tolbier/semaforo_ruido/PCBs/leds_PCB/leds_PCB_etch_copper_bottom.jpg

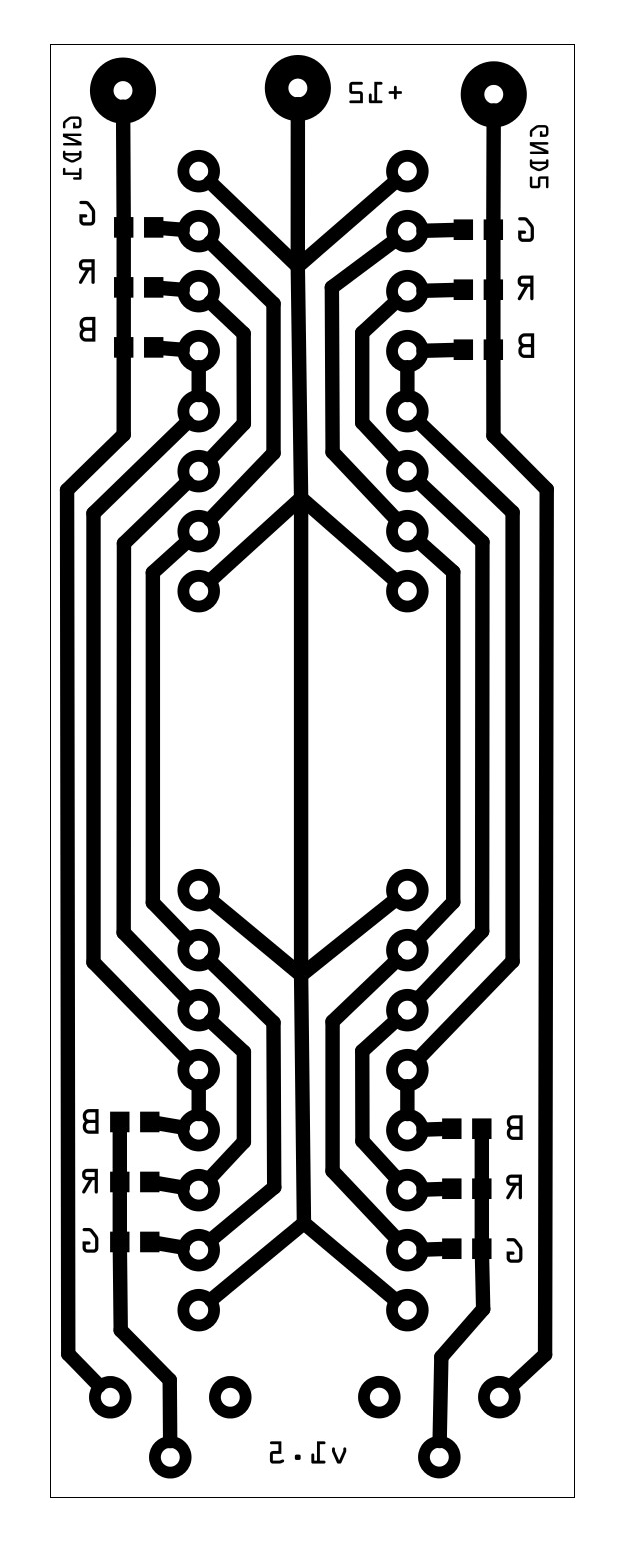
PCBs/leds_PCB/leds_PCB_etch_copper_bottom.jpg
