tolbier/semaforo_ruido/PCBs/leds_PCB/leds_PCB_pcb.jpg

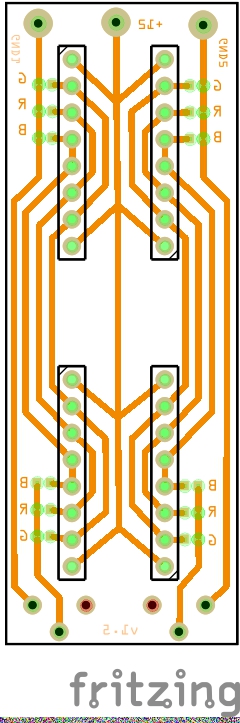
PCBs/leds_PCB/leds_PCB_pcb.jpg
