tolbier/semaforo_ruido/PCBs/semaforo_ruido_MainPCB/semaforo_ruido_MainPCB_esquema.jpg

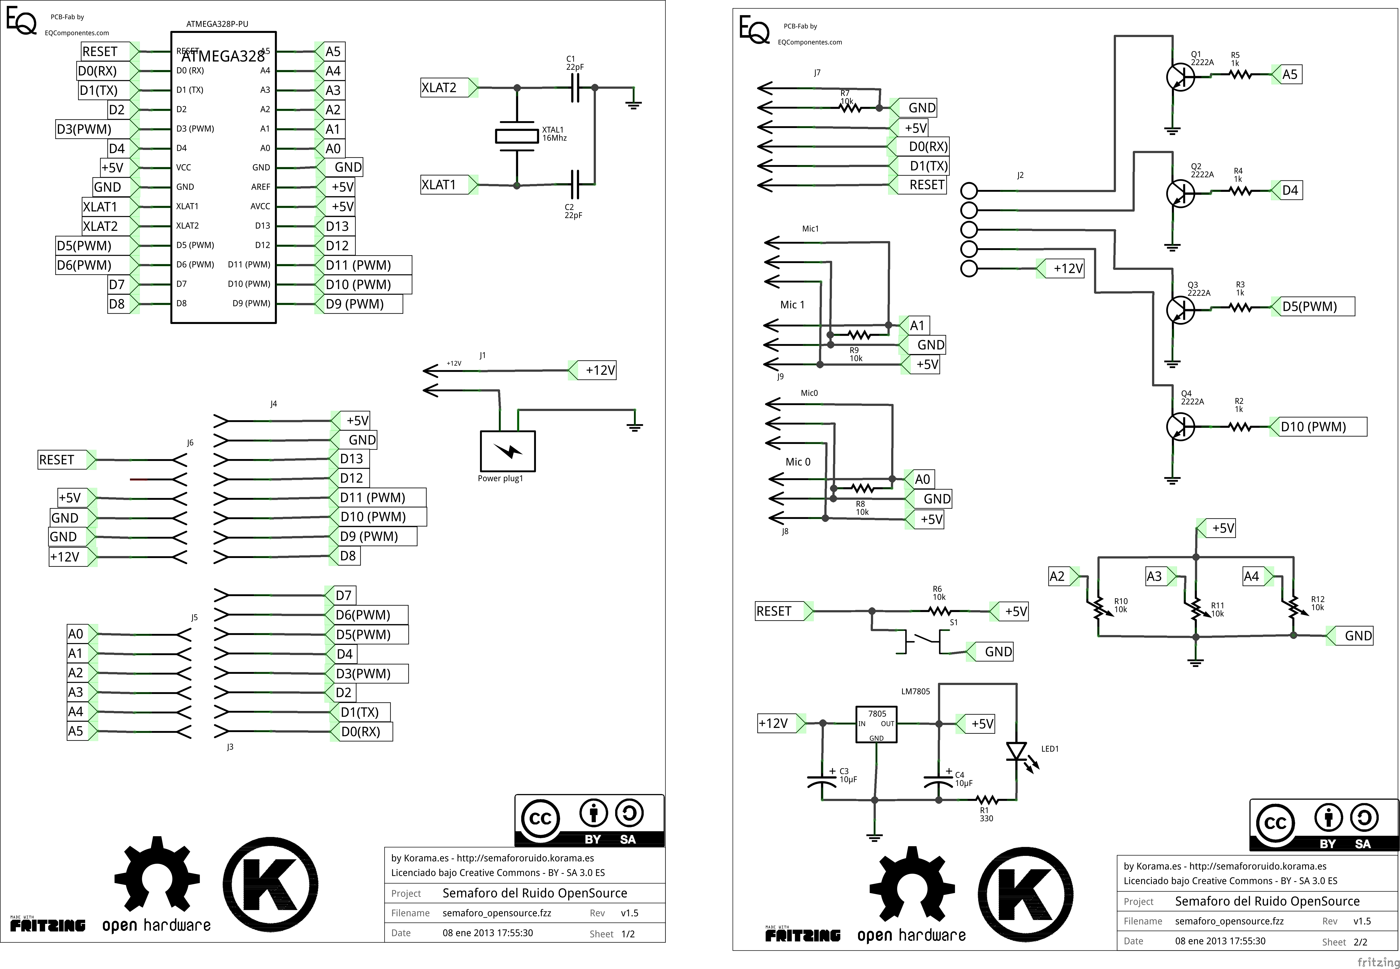
PCBs/semaforo_ruido_MainPCB/semaforo_ruido_MainPCB_esquema.jpg
