tolbier/semaforo_ruido/PCBs/semaforo_ruido_MainPCB/semaforo_ruido_MainPCB_etch_copper_bottom.jpg

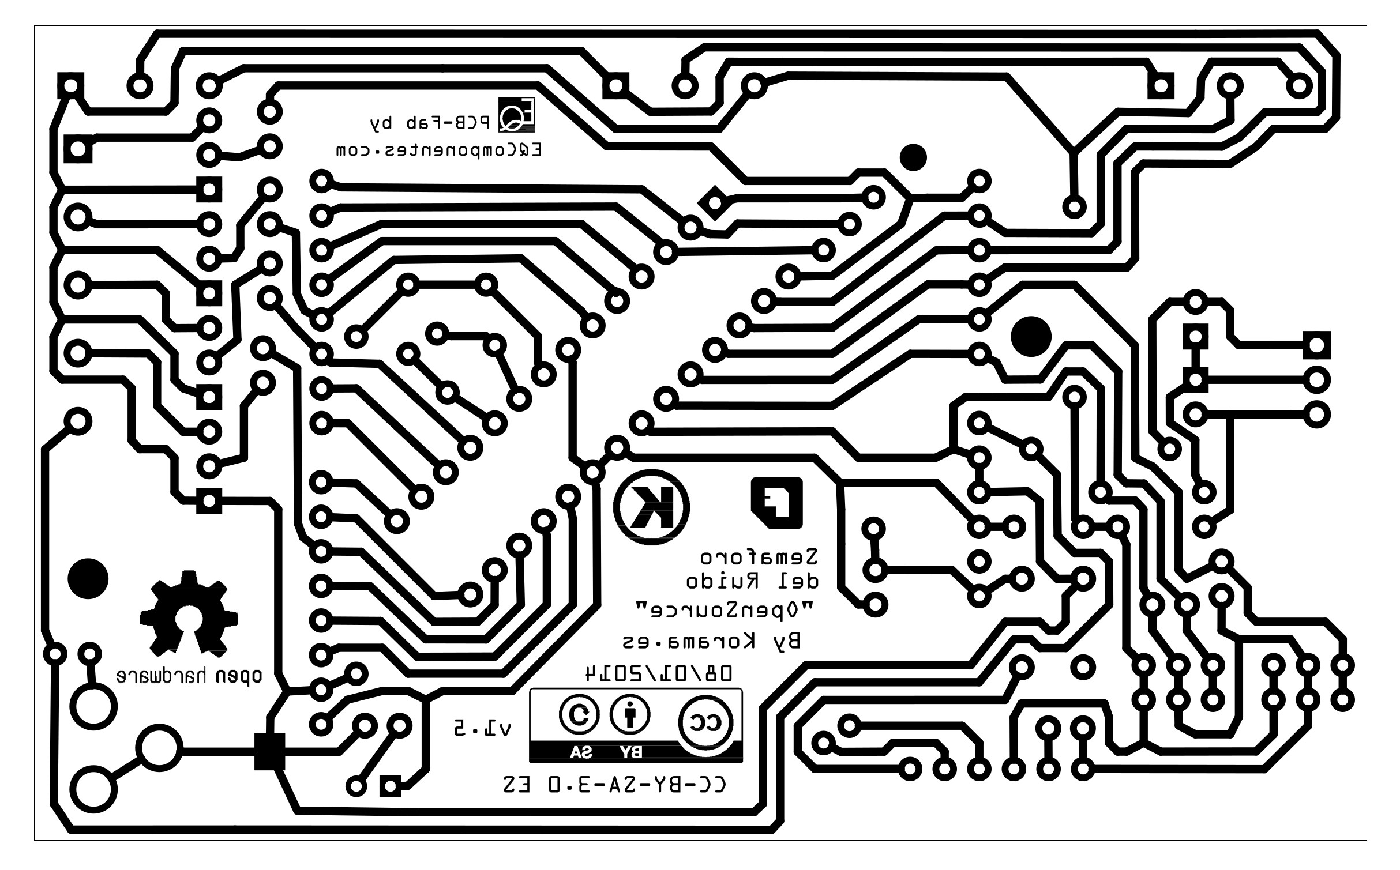
PCBs/semaforo_ruido_MainPCB/semaforo_ruido_MainPCB_etch_copper_bottom.jpg
