tolbier/semaforo_ruido/PCBs/semaforo_ruido_MainPCB/semaforo_ruido_MainPCB_pcb.jpg

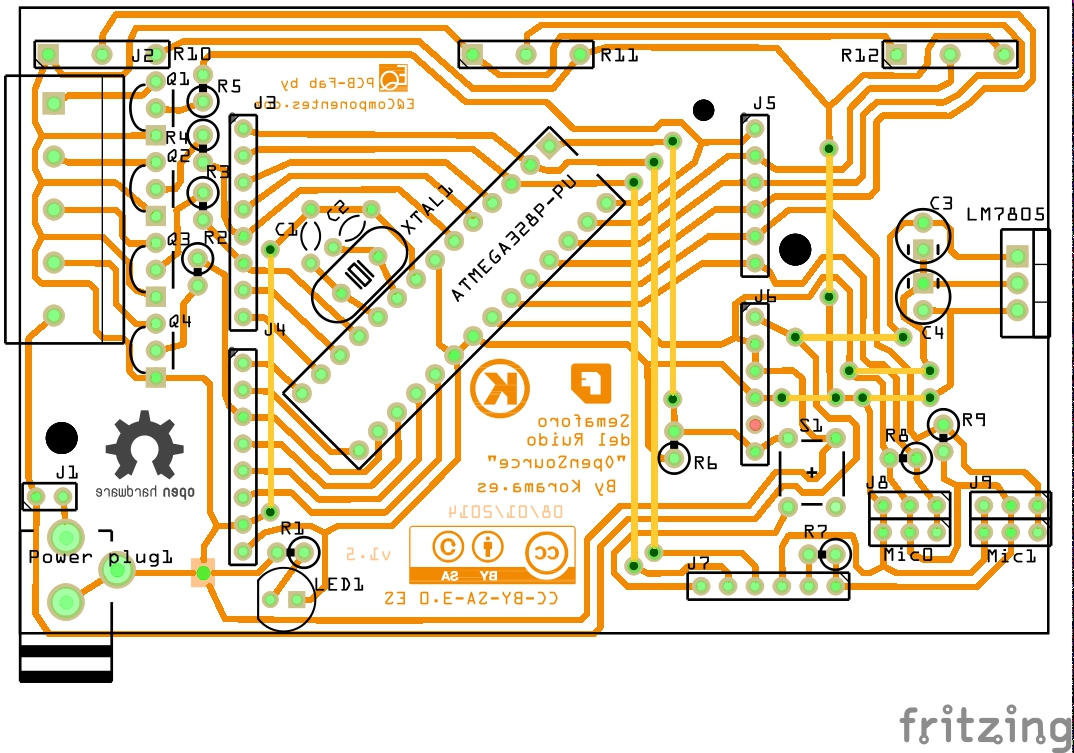
PCBs/semaforo_ruido_MainPCB/semaforo_ruido_MainPCB_pcb.jpg
