tolbier/semaforo_ruido/PCBs/wired_sensor_PCB/thumbs/wired_sensor_PCB_esquema.thumb.jpg

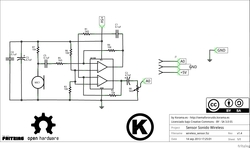
PCBs/wired_sensor_PCB/thumbs/wired_sensor_PCB_esquema.thumb.jpg
