tolbier/semaforo_ruido/PCBs/wired_sensor_PCB/thumbs/wired_sensor_PCB_etch_copper_bottom.thumb.jpg

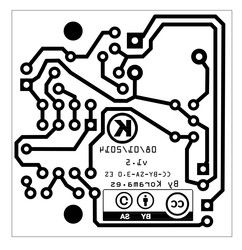
PCBs/wired_sensor_PCB/thumbs/wired_sensor_PCB_etch_copper_bottom.thumb.jpg
