tolbier/semaforo_ruido/PCBs/wired_sensor_PCB/thumbs/wired_sensor_PCB_pcb.thumb.jpg

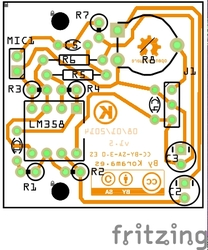
PCBs/wired_sensor_PCB/thumbs/wired_sensor_PCB_pcb.thumb.jpg
