tolbier/semaforo_ruido/tutoriales/images/material_necesario/cables_puente_hembra_hembra.jpg

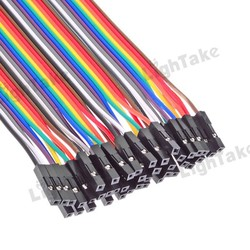
tutoriales/images/material_necesario/cables_puente_hembra_hembra.jpg
