tolbier/semaforo_ruido/tutoriales/images/material_necesario/cables_puente_macho_macho.jpg

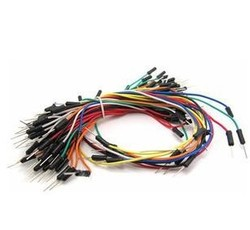
tutoriales/images/material_necesario/cables_puente_macho_macho.jpg
