tolbier/semaforo_ruido/tutoriales/images/material_necesario/juego_alicates_electrónica.jpg

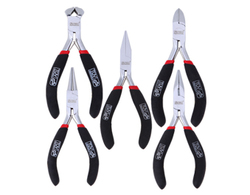
tutoriales/images/material_necesario/juego_alicates_electrónica.jpg
