tolbier/semaforo_ruido/tutoriales/images/material_necesario/polimetrodigital.jpg

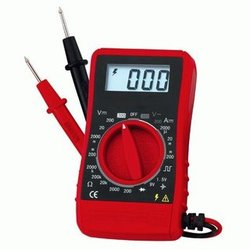
tutoriales/images/material_necesario/polimetrodigital.jpg
