tolbier/semaforo_ruido/tutoriales/images/material_necesario/rollo_estaño.jpg

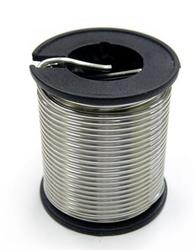
tutoriales/images/material_necesario/rollo_estaño.jpg
