tolbier/semaforo_ruido/tutoriales/images/material_necesario/soldador_estaño.jpg

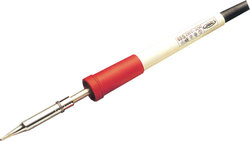
tutoriales/images/material_necesario/soldador_estaño.jpg
