tolbier/semaforo_ruido/tutoriales/images/wired_sensor_PCB_images/2pines_macho.png

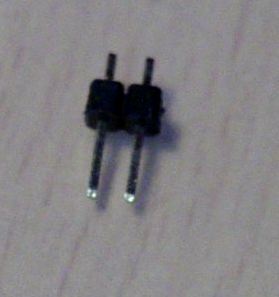
tutoriales/images/wired_sensor_PCB_images/2pines_macho.png
