tolbier/semaforo_ruido/tutoriales/images/wired_sensor_PCB_images/cond_4,7uF.png

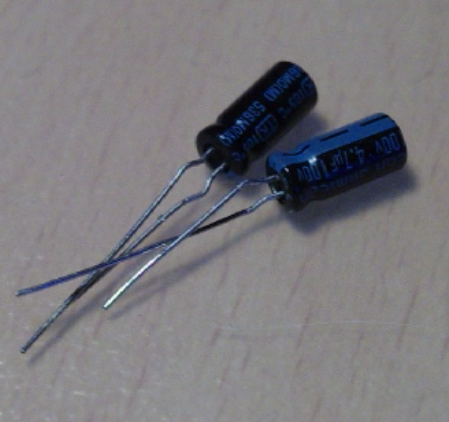
tutoriales/images/wired_sensor_PCB_images/cond_4,7uF.png
