tolbier/semaforo_ruido/tutoriales/images/wired_sensor_PCB_images/cond_100nf.png

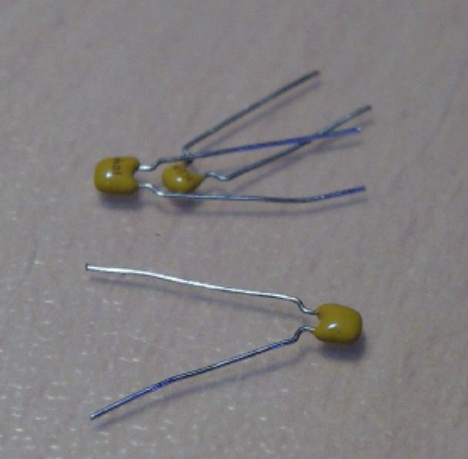
tutoriales/images/wired_sensor_PCB_images/cond_100nf.png
