tolbier/semaforo_ruido/tutoriales/images/wired_sensor_PCB_images/lm358.png

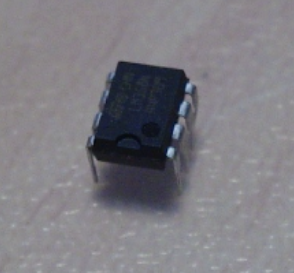
tutoriales/images/wired_sensor_PCB_images/lm358.png
