tolbier/semaforo_ruido/tutoriales/images/wired_sensor_PCB_images/micro_electret_y_conector.png

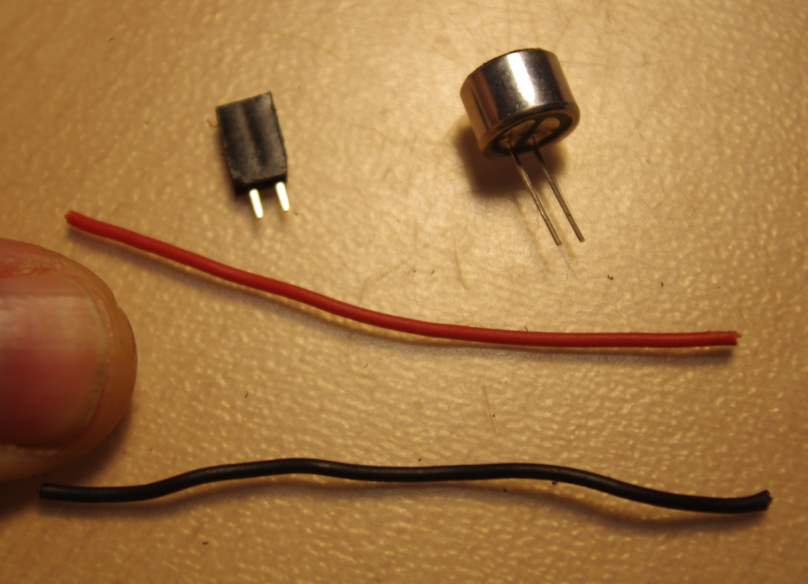
tutoriales/images/wired_sensor_PCB_images/micro_electret_y_conector.png
