tolbier/semaforo_ruido/tutoriales/images/wired_sensor_PCB_images/pcb_wired_sensor.png

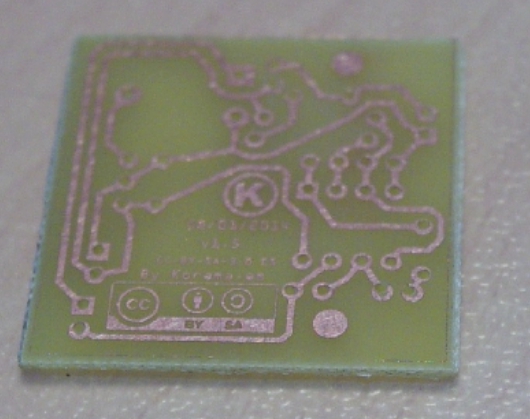
tutoriales/images/wired_sensor_PCB_images/pcb_wired_sensor.png
