tolbier/semaforo_ruido/tutoriales/images/wired_sensor_PCB_images/poste_polar_macho3pines.png

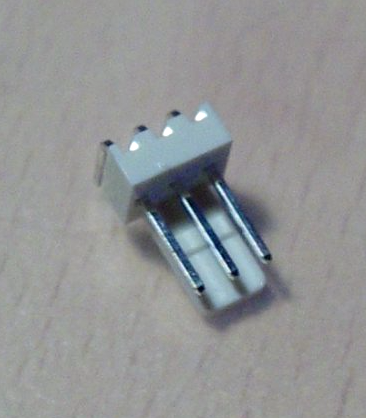
tutoriales/images/wired_sensor_PCB_images/poste_polar_macho3pines.png
