tolbier/semaforo_ruido/tutoriales/images/wired_sensor_PCB_images/pot_4,7k.png

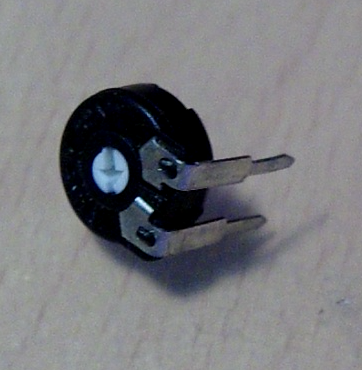
tutoriales/images/wired_sensor_PCB_images/pot_4,7k.png
