tolbier/semaforo_ruido/tutoriales/images/wired_sensor_PCB_images/res_10k.png

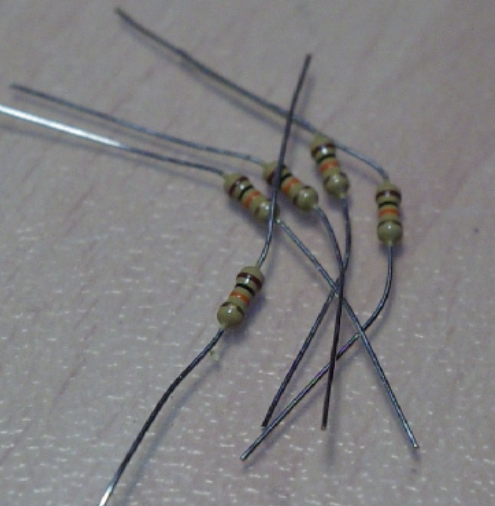
tutoriales/images/wired_sensor_PCB_images/res_10k.png
