tolbier/semaforo_ruido/tutoriales/images/wired_sensor_PCB_images/step3bis.png

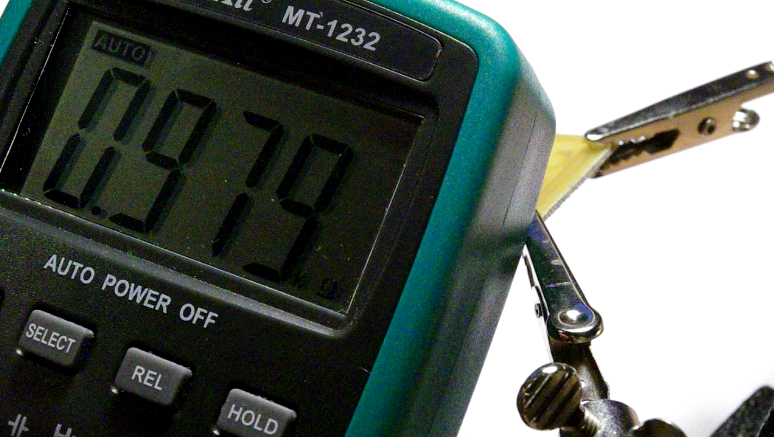
tutoriales/images/wired_sensor_PCB_images/step3bis.png
