tolbier/semaforo_ruido/tutoriales/images/wired_sensor_PCB_images/step13.png

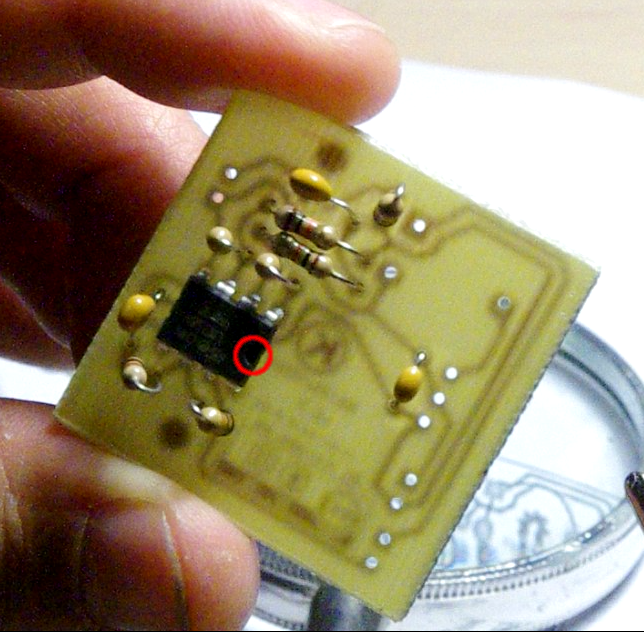
tutoriales/images/wired_sensor_PCB_images/step13.png
