tolbier/semaforo_ruido/tutoriales/images/wired_sensor_PCB_images/step14.png

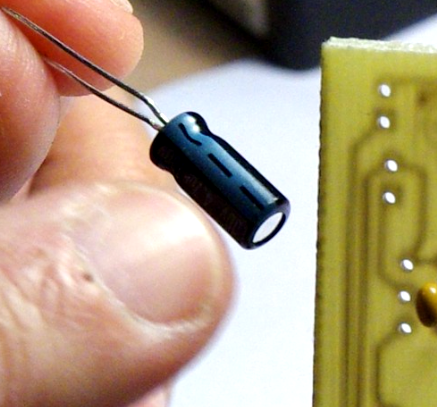
tutoriales/images/wired_sensor_PCB_images/step14.png
