tolbier/semaforo_ruido/tutoriales/images/wired_sensor_PCB_images/step23.png

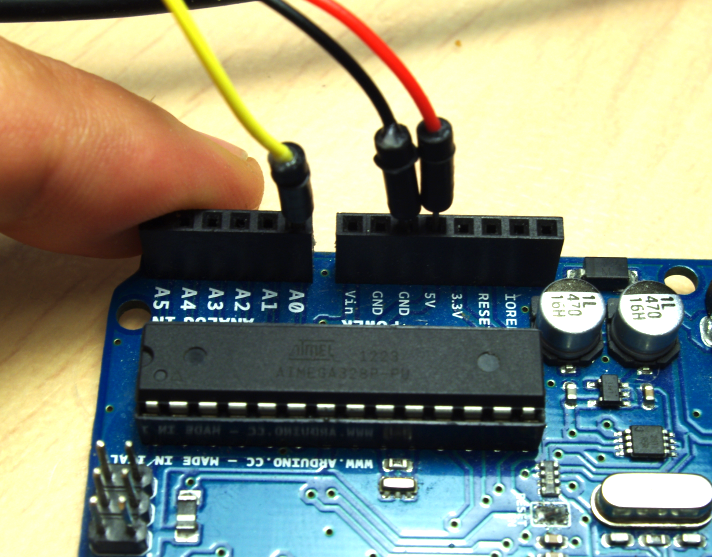
tutoriales/images/wired_sensor_PCB_images/step23.png
