tolbier/semaforo_ruido/tutoriales/images/wired_sensor_PCB_images/step_final.png

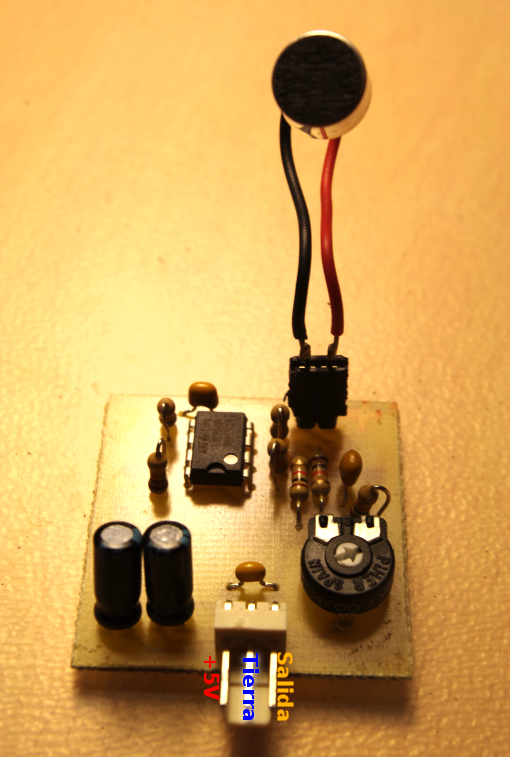
tutoriales/images/wired_sensor_PCB_images/step_final.png
