tolbier/semaforo_ruido/tutoriales/images/wired_sensor_PCB_images/tabla_resistencias.jpg

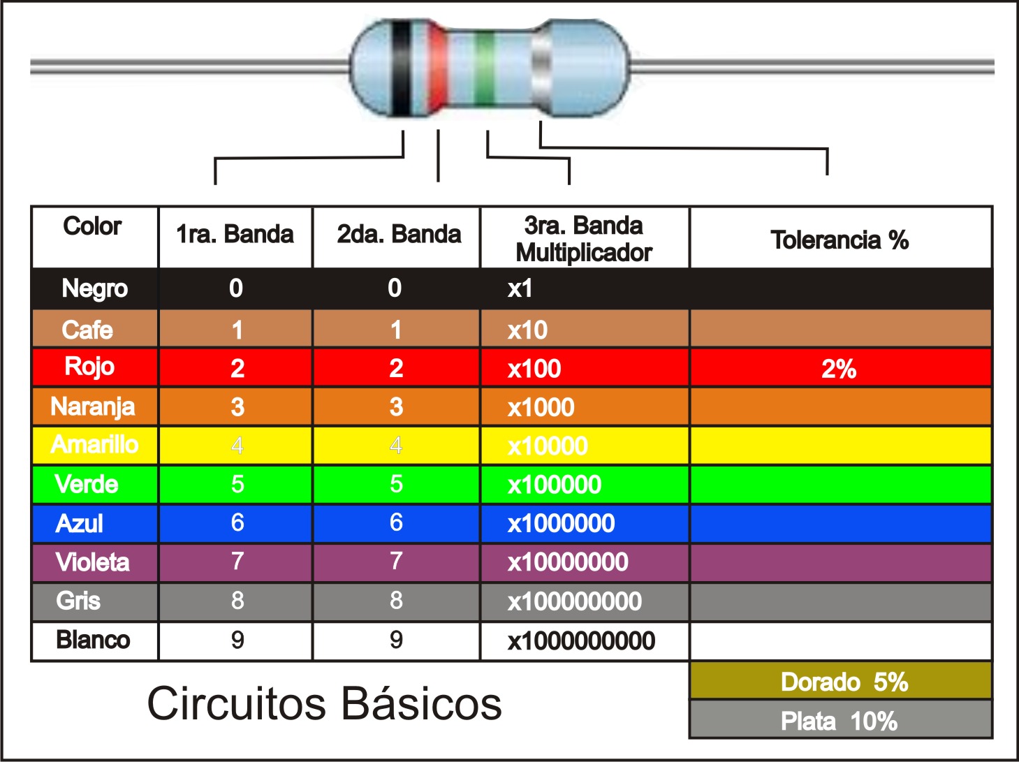
tutoriales/images/wired_sensor_PCB_images/tabla_resistencias.jpg
