tolbier/semaforo_ruido/tutoriales/images/wired_sensor_PCB_images/thumbs/step24.thumb.png

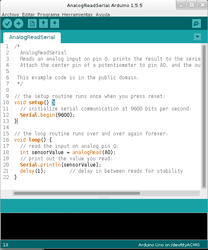
tutoriales/images/wired_sensor_PCB_images/thumbs/step24.thumb.png
