tolbier/semaforo_ruido/tutoriales/images/wired_sensor_PCB_images/video1_embed.png

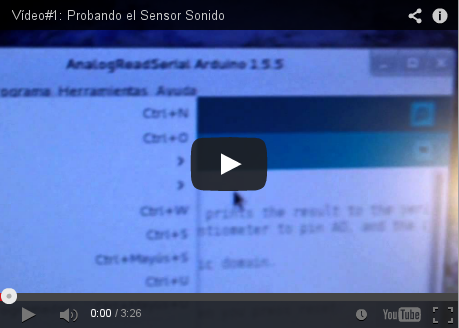
tutoriales/images/wired_sensor_PCB_images/video1_embed.png
