tolbier/semaforo_ruido/PCBs/wired_sensor_PCB/wired_sensor_PCB_pcb.pdf

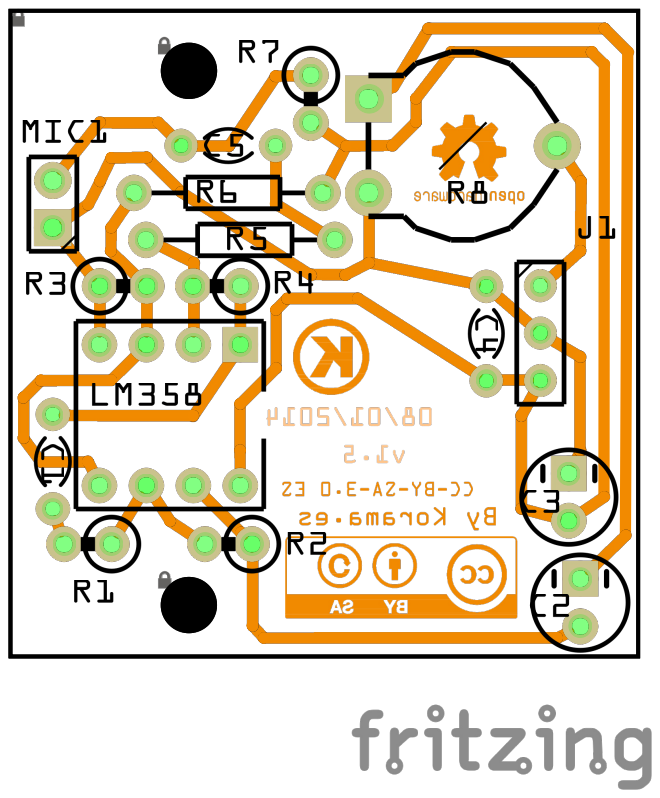
[picture p65: page 1]
